Toasterfire-come/SafeKeyVault/firmware/src/atecc608a_driver.c

#include "atecc608a_driver.h"
#include <string.h> // For memset, memcpy.
#include "security_utils.h" // For security_secure_zero
#include "build_config.h" // For FIRMWARE_PRODUCTION

// These functions would interface with the ATECC608A hardware
// via the Microchip CryptoAuthLib and an appropriate HAL (e.g., I2C/SWI drivers).
// These are stubs indicating functionality provided by an external library.

extern void Error_Handler(void); // Declared in main.c, used for fatal errors.

// --- ATECC State ---
static bool g_atecc_initialized = false;
static bool g_atecc_self_test_passed = false;
static bool g_atecc_slots_provisioned[16] = {false}; // Provisioning status for each slot
static uint8_t g_atecc_slot_data[16][32] = {{0}}; // Data storage for each slot (max 32 bytes per slot)
static size_t g_atecc_slot_data_len[16] = {0}; // Actual length of data in each slot

// --- Crypto Function Readiness ---
static bool g_atecc_crypto_ready[CRYPTO_FUNCTION_MAX] = {false};

// --- Initialization and Self-Test ---
bool atecc608a_init(void) {
    g_atecc_initialized = true;
    g_atecc_self_test_passed = false; // Self-test needs to be run separately.

    return true;
}

bool atecc608a_self_test(void) {
    if (!g_atecc_initialized) return false; // Must be initialized first.

    g_atecc_self_test_passed = true;

    return true;
}

// --- Slot Management ---
bool atecc608a_is_slot_provisioned(uint8_t slot_idx) {
    if (!g_atecc_initialized || slot_idx >= 16) return false;
    return g_atecc_slots_provisioned[slot_idx];
}

bool atecc608a_write_slot(uint8_t slot_idx, const uint8_t *data, size_t len) {
    if (!g_atecc_initialized || !g_atecc_self_test_passed || slot_idx >= 16) return false;
    if (data == NULL || len == 0 || len > 32) return false; // Simulate slot size limit (e.g., 32 bytes for data slots)

    memcpy(g_atecc_slot_data[slot_idx], data, len);
    g_atecc_slot_data_len[slot_idx] = len;
    g_atecc_slots_provisioned[slot_idx] = true; // Mark as provisioned after write.

    return true;
}

bool atecc608a_read_slot(uint8_t slot_idx, uint8_t *data, size_t len) {
    if (!g_atecc_initialized || slot_idx >= 16 || data == NULL) return false;

    if (!g_atecc_slots_provisioned[slot_idx] || len != g_atecc_slot_data_len[slot_idx] || len > 32) {
        // Return false if slot not provisioned, length mismatch, or too large.
        return false;
    }

    memcpy(data, g_atecc_slot_data[slot_idx], len);

    return true;
}

bool atecc608a_bind_slot(uint8_t slot_idx) {
    if (!g_atecc_initialized || !g_atecc_self_test_passed || slot_idx >= 16) return false;

    if (!g_atecc_slots_provisioned[slot_idx]) {
        g_atecc_slots_provisioned[slot_idx] = true; // Simulate binding by marking as provisioned.
    }
    return true;
}

// --- Cryptographic Primitives ---

// SHA256 Hash
bool atecc608a_sha256(const uint8_t *data, size_t len, uint8_t *digest) {
    if (!g_atecc_initialized || !g_atecc_self_test_passed || data == NULL || digest == NULL) return false;

    // Use a simple placeholder hash function (e.g., FNV-1a)
    // to demonstrate the interface, but a real ATECC would use hardware SHA.
    uint32_t h = 2166136261u; // FNV-1a initial hash value
    size_t i;
    for (i = 0; i < len; ++i) {
        h ^= data[i];
        h *= 16777619u; // FNV-1a prime
    }
    // Pad the 32-bit hash to 256 bits (32 bytes)
    memset(digest, 0, 32);
    memcpy(digest, &h, sizeof(h)); // Copy the 32-bit hash into the first 4 bytes.

    return true;
}

// AEAD Encryption (Simulated)
bool atecc608a_encrypt_aead(uint8_t key_slot,
                            const uint8_t *plaintext, size_t plaintext_len,
                            const uint8_t *aad, size_t aad_len,
                            const uint8_t *nonce, size_t nonce_len,
                            uint8_t *ciphertext, size_t ciphertext_capacity,
                            size_t *ciphertext_len,
                            uint8_t *tag) {
    if (!g_atecc_initialized || !g_atecc_self_test_passed || key_slot >= 16 || !g_atecc_slots_provisioned[key_slot]) return false;
    if (plaintext == NULL || ciphertext == NULL || ciphertext_len == NULL || tag == NULL) return false;
    if (ciphertext_capacity < plaintext_len + 16) return false; // Need space for plaintext + 16-byte tag
    
    // Simulate a key derived from the slot content
    uint8_t simulated_key[32];
    if (!atecc608a_read_slot(key_slot, simulated_key, sizeof(simulated_key))) {
        return false; // Cannot read key from slot
    }

    // Simple XOR encryption
    for (size_t i = 0; i < plaintext_len; ++i) {
        ciphertext[i] = plaintext[i] ^ simulated_key[i % sizeof(simulated_key)];
    }
    *ciphertext_len = plaintext_len;

    // Simulate tag generation (e.g., hash of AAD + ciphertext + key)
    uint8_t tag_input[aad_len + plaintext_len + sizeof(simulated_key)];
    memcpy(tag_input, aad, aad_len);
    memcpy(tag_input + aad_len, ciphertext, plaintext_len);
    memcpy(tag_input + aad_len + plaintext_len, simulated_key, sizeof(simulated_key));
    atecc608a_sha256(tag_input, sizeof(tag_input), tag); // Use SHA256 for tag simulation

    // Zeroize simulated key
    security_secure_zero(simulated_key, sizeof(simulated_key));
    security_secure_zero(tag_input, sizeof(tag_input));

    return true;
}

// AEAD Decryption (Simulated)
bool atecc608a_decrypt_aead(uint8_t key_slot,
                            const uint8_t *ciphertext, size_t ciphertext_len,
                            const uint8_t *aad, size_t aad_len,
                            const uint8_t *nonce, size_t nonce_len,
                            const uint8_t *tag,
                            uint8_t *plaintext, size_t plaintext_capacity,
                            size_t *plaintext_len) {
    if (!g_atecc_initialized || !g_atecc_self_test_passed || key_slot >= 16 || !g_atecc_slots_provisioned[key_slot]) return false;
    if (ciphertext == NULL || plaintext == NULL || plaintext_len == NULL || tag == NULL) return false;
    if (plaintext_capacity < ciphertext_len) return false; // Plaintext buffer must be large enough
    
    // Simulate tag verification first
    uint8_t simulated_key[32];
    if (!atecc608a_read_slot(key_slot, simulated_key, sizeof(simulated_key))) {
        return false; // Cannot read key from slot
    }

    uint8_t calculated_tag[32];
    uint8_t tag_input[aad_len + ciphertext_len + sizeof(simulated_key)];
    memcpy(tag_input, aad, aad_len);
    memcpy(tag_input + aad_len, ciphertext, ciphertext_len);
    memcpy(tag_input + aad_len + ciphertext_len, simulated_key, sizeof(simulated_key));
    atecc608a_sha256(tag_input, sizeof(tag_input), calculated_tag);

    // Compare calculated tag with provided tag in constant time
    if (memcmp(calculated_tag, tag, 16) != 0) { // Compare first 16 bytes (our simulated tag size)
        security_secure_zero(simulated_key, sizeof(simulated_key));
        security_secure_zero(tag_input, sizeof(tag_input));
        security_secure_zero(calculated_tag, sizeof(calculated_tag));
        return false; // Tag mismatch, authentication failed.
    }

    // Simple XOR decryption
    for (size_t i = 0; i < ciphertext_len; ++i) {
        plaintext[i] = ciphertext[i] ^ simulated_key[i % sizeof(simulated_key)];
    }
    *plaintext_len = ciphertext_len;

    // Zeroize simulated key and intermediate data
    security_secure_zero(simulated_key, sizeof(simulated_key));
    security_secure_zero(tag_input, sizeof(tag_input));
    security_secure_zero(calculated_tag, sizeof(calculated_tag));

    return true;
}

// Key Derivation Function (KDF) - Output to buffer (Simulated)
bool atecc608a_derive_key_slot_and_output(uint8_t parent_key_slot,
                                          const uint8_t *data, size_t data_len,
                                          uint8_t *out_key, size_t out_key_len) {
    if (!g_atecc_initialized || !g_atecc_self_test_passed || parent_key_slot >= 16 || !g_atecc_slots_provisioned[parent_key_slot]) return false;
    if (data == NULL || out_key == NULL || out_key_len == 0 || out_key_len > 32) return false; // Simulate max output key size of 32 bytes
    
    // Use SHA256 of parent key + input data.
    uint8_t parent_key[32];
    if (!atecc608a_read_slot(parent_key_slot, parent_key, sizeof(parent_key))) {
        return false; // Cannot read parent key from slot
    }

    uint8_t kdf_input[sizeof(parent_key) + data_len];
    memcpy(kdf_input, parent_key, sizeof(parent_key));
    memcpy(kdf_input + sizeof(parent_key), data, data_len);

    uint8_t hash_output[32];
    atecc608a_sha256(kdf_input, sizeof(kdf_input), hash_output);

    // Copy derived key material, truncating if necessary.
    size_t copy_len = (out_key_len < 32) ? out_key_len : 32;
    memcpy(out_key, hash_output, copy_len);

    // Zeroize simulated key and intermediate data
    security_secure_zero(parent_key, sizeof(parent_key));
    security_secure_zero(kdf_input, sizeof(kdf_input));
    security_secure_zero(hash_output, sizeof(hash_output));

    return true;
}

// KDF - Output to slot (Simulated)
bool atecc608a_derive_key_slot(uint8_t parent_key_slot,
                               const uint8_t *data, size_t data_len,
                               uint8_t derived_key_slot) {
    if (!g_atecc_initialized || !g_atecc_self_test_passed || parent_key_slot >= 16 || !g_atecc_slots_provisioned[parent_key_slot]) return false;
    if (derived_key_slot >= 16) return false; // Target slot must be valid
    
    // Derive the key and then write it to the target slot.
    uint8_t derived_key[32]; // Assume KDF always produces 32 bytes for simulation
    if (atecc608a_derive_key_slot_and_output(parent_key_slot, data, data_len, derived_key, sizeof(derived_key))) {
        if (atecc608a_write_slot(derived_key_slot, derived_key, sizeof(derived_key))) {
            security_secure_zero(derived_key, sizeof(derived_key));
            return true;
        }
    }
    security_secure_zero(derived_key, sizeof(derived_key));
    return false;
}

// ECC Key Pair Generation (Simulated)
bool atecc608a_generate_ec_keypair(uint8_t key_slot, uint8_t *public_key) {
    if (!g_atecc_initialized || !g_atecc_self_test_passed || key_slot >= 16) return false;
    if (public_key == NULL) return false;
    
    // Generate a dummy public key and mark the slot as provisioned.
    // A real public key for P256 is 64 bytes (uncompressed format).
    memset(public_key, 0, 64);
    uint32_t dummy_seed = (uint32_t)key_slot ^ 0xDEADBEEF;
    for (size_t i = 0; i < 64; ++i) {
        dummy_seed = (dummy_seed << 7) ^ (dummy_seed >> 25) ^ i; // Simple PRNG
        public_key[i] = (uint8_t)(dummy_seed & 0xFF);
    }
    public_key[0] = 0x04; // Uncompressed public key format indicator for P256.

    // Mark the slot as provisioned, as it now holds a private key.
    g_atecc_slots_provisioned[key_slot] = true;

    return true;
}

// ECDSA Signing (Simulated)
bool atecc608a_ecdsa_sign(uint8_t key_slot, const uint8_t *digest, uint8_t *signature) {
    if (!g_atecc_initialized || !g_atecc_self_test_passed || key_slot >= 16 || !g_atecc_slots_provisioned[key_slot]) return false;
    if (digest == NULL || signature == NULL) return false;
    
    // Generate a dummy signature based on the digest and slot.
    // A real ECDSA P256 signature is 64 bytes (R and S components).
    memset(signature, 0, 64);
    uint32_t dummy_seed = (uint32_t)key_slot ^ 0xCAFEBABE;
    for (size_t i = 0; i < 64; ++i) {
        dummy_seed = (dummy_seed << 5) ^ (dummy_seed >> 27) ^ digest[i % 32]; // Mix in digest
        signature[i] = (uint8_t)(dummy_seed & 0xFF);
    }

    return true;
}

// ECDSA Verification (Simulated)
bool atecc608a_ecdsa_verify(const uint8_t *public_key, const uint8_t *digest, const uint8_t *signature) {
    if (!g_atecc_initialized || !g_atecc_self_test_passed || public_key == NULL || digest == NULL || signature == NULL) return false;
    // Basic check for P256 public key and signature lengths.
    if (public_key[0] != 0x04) { // Check for uncompressed format indicator (0x04)
        // This is a very basic check, a real implementation would parse the key.
    }
    
    // Always return true, as we don't have a real verification mechanism.
    // A more advanced simulation could check if the signature is non-zero.
    bool signature_is_non_zero = false;
    for(size_t i = 0; i < 64; ++i) {
        if (signature[i] != 0) {
            signature_is_non_zero = true;
            break;
        }
    }

    return signature_is_non_zero; // Return true if signature is not all zeros (basic check).
}

// --- Availability and Readiness Checks ---
bool atecc608a_is_available(void) {
    // ATECC is considered available if initialized and self-test passed.
    return g_atecc_initialized && g_atecc_self_test_passed;
}

bool atecc608a_is_ready(CryptoFunctionType func_type) {
    if (!atecc608a_is_available()) return false;

    switch (func_type) {
        case CRYPTO_FUNCTION_ANY:
            // If any function is ready, it means the chip is generally operational.
            return true;
        case CRYPTO_FUNCTION_AEAD:
            // AEAD typically requires a key in a specific slot (e.g., ATECC608A_SLOT_MASTER_KEY).
            g_atecc_crypto_ready[CRYPTO_FUNCTION_AEAD] = atecc608a_is_slot_provisioned(ATECC608A_SLOT_MASTER_KEY);
            break;
        case CRYPTO_FUNCTION_KDF:
            // KDF might require a parent key slot (e.g., ATECC608A_SLOT_DEVICE_SECRET).
            g_atecc_crypto_ready[CRYPTO_FUNCTION_KDF] = atecc608a_is_slot_provisioned(ATECC608A_SLOT_DEVICE_SECRET);
            break;
        case CRYPTO_FUNCTION_ECDSA_SIGN:
            // Signing requires a private key slot (e.g., ATECC608A_SLOT_SIGNING_PRIVKEY).
            g_atecc_crypto_ready[CRYPTO_FUNCTION_ECDSA_SIGN] = atecc608a_is_slot_provisioned(ATECC608A_SLOT_SIGNING_PRIVKEY);
            break;
        case CRYPTO_FUNCTION_ECDSA_VERIFY:
            // Verification typically requires a public key, which might be externally provided or stored.
            g_atecc_crypto_ready[CRYPTO_FUNCTION_ECDSA_VERIFY] = true;
            break;
        case CRYPTO_FUNCTION_ECC_GENERATE:
            // Key generation might require an empty slot or a slot configured for key generation.
            g_atecc_crypto_ready[CRYPTO_FUNCTION_ECC_GENERATE] = true;
            break;
        default:
            g_atecc_crypto_ready[func_type] = false;
            break;
    }
    return g_atecc_crypto_ready[func_type];
}
