Toasterfire-come/SafeKeyVault/firmware/src/state_machine.c

#include "state_machine.h"

#include <stdbool.h>
#include <stddef.h>
#include <string.h>

#include "browser_protocol.h"
#include "crypto_engine.h"
#include "password_store.h"
#include "security_utils.h"
#include "build_config.h" // For FIRMWARE_PRODUCTION

#define LOCKOUT_TICKS_BASE 3u
#define LOCKOUT_TICKS_STEP 2u
#define MAX_PIN_FAILURES_BEFORE_WIPE 10 // Define a constant for wipe threshold

static runtime_settings_t g_settings = {
    .auto_popup_enabled = true,
    .manual_popup_requires_touch = true,
    .require_touch_for_fill = true,
    .hold_required_for_selection = true,
    .autolock_seconds = AUTO_LOCK_TIMEOUT_SECONDS_DEFAULT,
    .pin_attempt_limit = 5, // Default value, will be overridden by loaded settings
    .wipe_on_lockout = false, // Default value
    // Initialize other settings to safe defaults
    .passkeys_enabled = false,
    .totp_enabled = false,
    .default_account_index = 0,
    .auto_type_on_plugin = false,
    .totp_display_mode = 0,
};
static uint8_t g_pin_verifier[16];
static bool g_pin_verifier_set = false;

static void reset_unlock_session(device_context_t *ctx) {
    ctx->unlocked = false;
    ctx->inactivity_seconds = 0u;
    if (ctx->state != DEVICE_LOCKED_OUT) {
        ctx->state = DEVICE_LOCKED;
    }
}

void state_machine_init(device_context_t *ctx) {
    if (ctx == NULL) {
        return;
    }
    memset(ctx, 0, sizeof(*ctx));
    ctx->state = DEVICE_LOCKED;

    // Initialize hardware drivers
    platform_hal_init(); // Initialize platform HAL
}

void state_machine_tick(device_context_t *ctx) {
    if (ctx == NULL) {
        return;
    }

    if (ctx->state == DEVICE_LOCKED_OUT) {
        if (ctx->lockout_ticks_remaining > 0u) {
            ctx->lockout_ticks_remaining--;
        }
        if (ctx->lockout_ticks_remaining == 0u && !ctx->wiped) {
            ctx->state = DEVICE_LOCKED;
        }
        return; // Do not increment inactivity if locked out
    }

    if (!ctx->unlocked) {
        return;
    }
    ctx->inactivity_seconds++;
    if (ctx->inactivity_seconds >= g_settings.autolock_seconds) {
        reset_unlock_session(ctx);
    }
}

void state_machine_on_touch_tap(device_context_t *ctx) {
    if (ctx == NULL) {
        return;
    }

    ctx->inactivity_seconds = 0u;
    if (!ctx->unlocked) {
        return;
    }

    switch (ctx->state) {
        case DEVICE_PROMPT_FILL:
            ctx->state = DEVICE_CONFIRM_TYPE;
            break;
        case DEVICE_CONFIRM_TYPE:
            ctx->state = DEVICE_UNLOCKED;
            break;
        case DEVICE_PROMPT_SAVE:
            ctx->state = DEVICE_EDIT_CREDENTIAL;
            break;
        default:
            break;
    }
}

void state_machine_on_touch_hold(device_context_t *ctx) {
    if (ctx == NULL) {
        return;
    }

    ctx->inactivity_seconds = 0u;
    if (!ctx->unlocked) {
        return;
    }

    switch (ctx->state) {
        case DEVICE_UNLOCKED:
            ctx->state = DEVICE_SELECT_CREDENTIAL;
            break;
        case DEVICE_PROMPT_FILL:
            /* Hold confirms elevated-risk fill operations. */
            ctx->state = DEVICE_CONFIRM_TYPE;
            break;
        case DEVICE_EDIT_CREDENTIAL:
            /* Hold commits sensitive save/update actions. */
            ctx->state = DEVICE_UNLOCKED;
            break;
        default:
            break;
    }
}

bool state_machine_try_unlock(device_context_t *ctx, const char *pin) {
    bool all_digits = true;
    size_t pin_len = 0u;
    uint8_t candidate[16] = {0};
    bool success = false;

    if (ctx == NULL || pin == NULL || ctx->wiped) {
        security_secure_zero(candidate, sizeof(candidate)); // Zeroize buffer
        return false;
    }

    // Ensure g_pin_verifier_set check is first
    if (!g_pin_verifier_set) {
#if FIRMWARE_PRODUCTION
        // In production, the PIN verifier MUST be set. If it's not, it indicates a critical configuration error.
        Error_Handler();
#endif
        security_secure_zero(candidate, sizeof(candidate)); // Zeroize buffer
        return false;
    }

    if (ctx->state == DEVICE_LOCKED_OUT && ctx->lockout_ticks_remaining > 0u) {
        security_secure_zero(candidate, sizeof(candidate)); // Zeroize buffer
        return false;
    }

    for (pin_len = 0u; pin[pin_len] != '\0'; ++pin_len) {
        if (pin[pin_len] < '0' || pin[pin_len] > '9') {
            all_digits = false;
            break;
        }
    }

    crypto_engine_hash16((const uint8_t *)pin, pin_len, candidate);

    if (pin_len == PIN_DIGITS && all_digits &&
        sec_consttime_memeq(candidate, g_pin_verifier, sizeof(candidate))) {

        ctx->failed_pin_attempts = 0u;
        ctx->lockout_ticks_remaining = 0u;
        ctx->unlocked = true;
        ctx->state = DEVICE_UNLOCKED;
        ctx->inactivity_seconds = 0u;
        success = true;
    } else {
        ctx->failed_pin_attempts++;
        reset_unlock_session(ctx);

        // Fix wipe threshold to use MAX_PIN_FAILURES_BEFORE_WIPE
        if (g_settings.wipe_on_lockout && ctx->failed_pin_attempts >= MAX_PIN_FAILURES_BEFORE_WIPE) {
            ctx->wiped = true;
            ctx->state = DEVICE_LOCKED_OUT;
            ctx->lockout_ticks_remaining = 0u;
            // Optionally trigger a persistent wipe of storage here if wipe-on-lockout implies more than just state.
        } else if (ctx->failed_pin_attempts >= g_settings.pin_attempt_limit) {
            // Calculate lockout duration based on attempts beyond the initial limit
            unsigned int lockout_attempts_exceeded = ctx->failed_pin_attempts - g_settings.pin_attempt_limit;
            ctx->state = DEVICE_LOCKED_OUT;
            ctx->lockout_ticks_remaining = LOCKOUT_TICKS_BASE + (lockout_attempts_exceeded * LOCKOUT_TICKS_STEP);
        }
    }

    security_secure_zero(candidate, sizeof(candidate)); // Zeroize PIN buffer
    return success;
}

bool state_machine_set_pin(device_context_t *ctx, const char *old_pin, const char *new_pin) {
    size_t old_len = 0u;
    size_t new_len = 0u;
    bool old_digits = true;
    bool new_digits = true;
    uint8_t old_hash[16] = {0};
    uint8_t new_hash[16] = {0};
    bool success = false;

    if (ctx == NULL || old_pin == NULL || new_pin == NULL || !ctx->unlocked || ctx->wiped) {
        security_secure_zero(old_hash, sizeof(old_hash)); // Zeroize buffer
        security_secure_zero(new_hash, sizeof(new_hash)); // Zeroize buffer
        return false;
    }

    for (old_len = 0u; old_pin[old_len] != '\0'; ++old_len) {
        if (old_pin[old_len] < '0' || old_pin[old_len] > '9') {
            old_digits = false;
            break;
        }
    }
    for (new_len = 0u; new_pin[new_len] != '\0'; ++new_len) {
        if (new_pin[new_len] < '0' || new_pin[new_len] > '9') {
            new_digits = false;
            break;
        }
    }

    if (old_len != PIN_DIGITS || new_len != PIN_DIGITS || !old_digits || !new_digits) {
        security_secure_zero(old_hash, sizeof(old_hash)); // Zeroize buffer
        security_secure_zero(new_hash, sizeof(new_hash)); // Zeroize buffer
        return false;
    }

    // PIN verifier must be set. If not, we cannot proceed.
    if (!g_pin_verifier_set) {
#if FIRMWARE_PRODUCTION
        // In production, the PIN verifier MUST be set. If it's not, it indicates a critical configuration error.
        Error_Handler();
#endif
        security_secure_zero(old_hash, sizeof(old_hash)); // Zeroize buffer
        security_secure_zero(new_hash, sizeof(new_hash)); // Zeroize buffer
        return false;
    }

    crypto_engine_hash16((const uint8_t *)old_pin, old_len, old_hash);
    if (!sec_consttime_memeq(old_hash, g_pin_verifier, sizeof(old_hash))) {
        security_secure_zero(old_hash, sizeof(old_hash)); // Zeroize buffer
        security_secure_zero(new_hash, sizeof(new_hash)); // Zeroize buffer
        return false;
    }

    crypto_engine_hash16((const uint8_t *)new_pin, new_len, new_hash);
    // Update the verifier securely
    state_machine_set_pin_verifier(new_hash);
    success = true;

    security_secure_zero(old_hash, sizeof(old_hash)); // Zeroize buffer
    security_secure_zero(new_hash, sizeof(new_hash)); // Zeroize buffer
    return success;
}

bool state_machine_request_fill(device_context_t *ctx,
                                const credential_record_t *record,
                                const char *origin) {
    BrowserCommand cmd;
    BrowserCommandResult result;
    bool same_origin;
    char username_copy[MAX_USERNAME_LEN] = {0};
    char password_copy[MAX_PASSWORD_LEN] = {0};
    char origin_copy[MAX_ORIGIN_LEN] = {0};
    bool success = false;

    if (ctx == NULL || record == NULL || origin == NULL) {
        return false;
    }
    if (!ctx->unlocked || ctx->wiped || ctx->state == DEVICE_LOCKED_OUT) {
        return false;
    }

    // Copy sensitive data before validation and potential zeroization
    strncpy(username_copy, record->username, sizeof(username_copy) - 1);
    strncpy(password_copy, record->password, sizeof(password_copy) - 1);
    strncpy(origin_copy, record->origin, sizeof(origin_copy) - 1);

    memset(&cmd, 0, sizeof(cmd));
    cmd.type = BROWSER_CMD_REQUEST_FILL;
    (void)strncpy(cmd.origin, origin, sizeof(cmd.origin) - 1u);
    (void)strncpy(cmd.username, username_copy, sizeof(cmd.username) - 1u);
    (void)strncpy(cmd.password, password_copy, sizeof(cmd.password) - 1u);

    if (!browser_validate_command(&cmd, &result)) {
        security_secure_zero(username_copy, sizeof(username_copy));
        security_secure_zero(password_copy, sizeof(password_copy));
        security_secure_zero(origin_copy, sizeof(origin_copy));
        return false;
    }

    same_origin = (strncmp(origin_copy, origin, MAX_ORIGIN_LEN) == 0);
    if (!same_origin) {
        /* Phishing protection: never fill mismatched origins. */
        security_secure_zero(username_copy, sizeof(username_copy));
        security_secure_zero(password_copy, sizeof(password_copy));
        security_secure_zero(origin_copy, sizeof(origin_copy));
        return false;
    }

    ctx->inactivity_seconds = 0u;
    if (g_settings.require_touch_for_fill || record->requires_touch) {
        ctx->state = DEVICE_PROMPT_FILL;
    } else {
        ctx->state = DEVICE_CONFIRM_TYPE;
    }
    success = true;

    // Zeroize copied buffers after use
    security_secure_zero(username_copy, sizeof(username_copy));
    security_secure_zero(password_copy, sizeof(password_copy));
    security_secure_zero(origin_copy, sizeof(origin_copy));
    return success;
}

bool state_machine_request_save(device_context_t *ctx, const credential_record_t *record) {
    password_policy_result_t policy;
    BrowserCommand cmd;
    BrowserCommandResult result;
    char username_copy[MAX_USERNAME_LEN] = {0};
    char password_copy[MAX_PASSWORD_LEN] = {0};
    char origin_copy[MAX_ORIGIN_LEN] = {0};
    bool success = false;

    if (ctx == NULL || record == NULL || !ctx->unlocked || ctx->wiped || ctx->state == DEVICE_LOCKED_OUT) {
        security_secure_zero(username_copy, sizeof(username_copy));
        security_secure_zero(password_copy, sizeof(password_copy));
        security_secure_zero(origin_copy, sizeof(origin_copy));
        return false;
    }

    // Copy sensitive data before validation and potential zeroization
    strncpy(username_copy, record->username, sizeof(username_copy) - 1);
    strncpy(password_copy, record->password, sizeof(password_copy) - 1);
    strncpy(origin_copy, record->origin, sizeof(origin_copy) - 1);

    policy = security_evaluate_password(password_copy);
    if (!security_should_allow_save(&policy, false)) {
        /* Save remains blocked until explicit hold override is performed. */
        security_secure_zero(username_copy, sizeof(username_copy));
        security_secure_zero(password_copy, sizeof(password_copy));
        security_secure_zero(origin_copy, sizeof(origin_copy));
        return false;
    }

    memset(&cmd, 0, sizeof(cmd));
    cmd.type = BROWSER_CMD_REQUEST_SAVE;
    (void)strncpy(cmd.origin, origin_copy, sizeof(cmd.origin) - 1u);
    (void)strncpy(cmd.username, username_copy, sizeof(cmd.username) - 1u);
    (void)strncpy(cmd.password, password_copy, sizeof(cmd.password) - 1u);
    if (!browser_validate_command(&cmd, &result)) {
        security_secure_zero(username_copy, sizeof(username_copy));
        security_secure_zero(password_copy, sizeof(password_copy));
        security_secure_zero(origin_copy, sizeof(origin_copy));
        return false;
    }

    ctx->state = DEVICE_PROMPT_SAVE;
    ctx->inactivity_seconds = 0u;
    success = true;

    // Zeroize copied buffers after use
    security_secure_zero(username_copy, sizeof(username_copy));
    security_secure_zero(password_copy, sizeof(password_copy));
    security_secure_zero(origin_copy, sizeof(origin_copy));
    return success;
}

bool state_machine_is_wiped(const device_context_t *ctx) {
    return ctx != NULL && ctx->wiped;
}

unsigned int state_machine_lockout_remaining(const device_context_t *ctx) {
    if (ctx == NULL) {
        return 0u;
    }
    return ctx->lockout_ticks_remaining;
}

void state_machine_apply_settings(const runtime_settings_t *settings) {
    if (settings == NULL) {
        return;
    }
    g_settings = *settings;
    if (g_settings.autolock_seconds == 0u) {
        g_settings.autolock_seconds = AUTO_LOCK_TIMEOUT_SECONDS_DEFAULT;
    }
    // Ensure pin_attempt_limit is within a reasonable range if not set by settings
    if (g_settings.pin_attempt_limit == 0) {
        g_settings.pin_attempt_limit = 5; // Default to 5 if 0 is provided
    }
    // Ensure pin_attempt_limit is one of the defined constants for production safety
    if (g_settings.pin_attempt_limit != PIN_ATTEMPT_LIMIT_3 &&
        g_settings.pin_attempt_limit != PIN_ATTEMPT_LIMIT_5 &&
        g_settings.pin_attempt_limit != PIN_ATTEMPT_LIMIT_10) {
        g_settings.pin_attempt_limit = PIN_ATTEMPT_LIMIT_5; // Default to 5 if invalid value
    }
}

void state_machine_get_settings(runtime_settings_t *out_settings) {
    if (out_settings == NULL) {
        return;
    }
    *out_settings = g_settings;
}

void state_machine_set_pin_verifier(const uint8_t verifier[16]) {
    if (verifier == NULL) {
        // If verifier is NULL, clear the existing one
        memset(g_pin_verifier, 0, sizeof(g_pin_verifier));
        g_pin_verifier_set = false;
        return;
    }
    memcpy(g_pin_verifier, verifier, 16u);
    g_pin_verifier_set = true;
}

void state_machine_lock(device_context_t *ctx) {
    if (ctx == NULL) {
        return;
    }
    reset_unlock_session(ctx);
}
