Toasterfire-come/SafeKeyVault/firmware/src/common_passwords.c

#include "common_passwords.h"

const char *k_common_passwords[] = {
    "123456",
    "12345678",
    "123456789",
    "password",
    "qwerty",
    "qwerty123",
    "11111111",
    "abc123",
    "letmein",
    "admin",
    "welcome",
    "iloveyou",
    "password1",
    "123123123",
    "00000000"
};

const size_t k_common_passwords_count =
    sizeof(k_common_passwords) / sizeof(k_common_passwords[0]);
